alexBinos/tkl_keyboard/Mechanical/v0/tkl_bottom_middle.STL

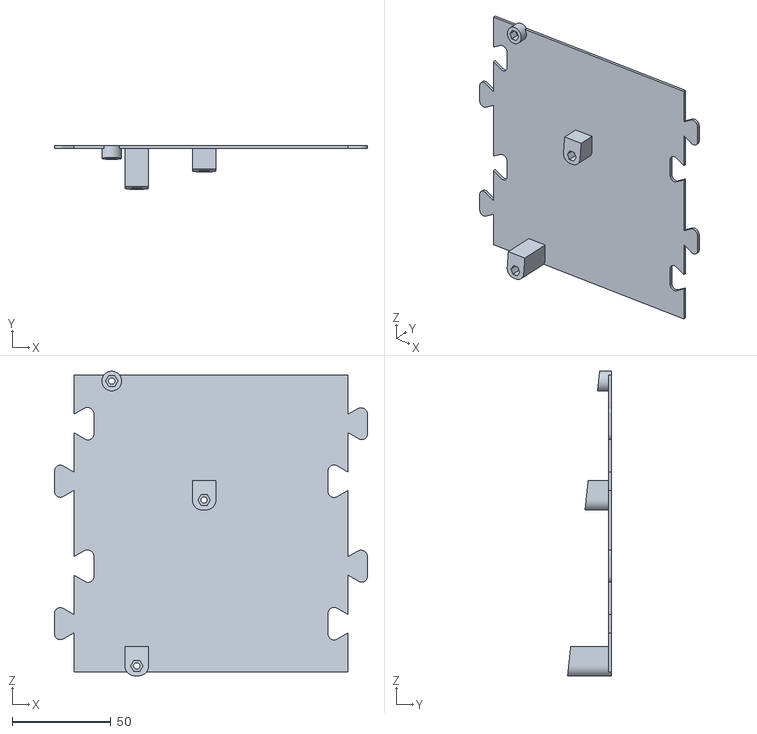
[picture p16: CAD file, 2022-05-21, an earlier design]
Mechanical/v0/tkl_bottom_middle.STL
158.7 x 22.2 x 154.5
