alexBinos/tkl_keyboard/Mechanical/v0/tkl_bottom_right.STL

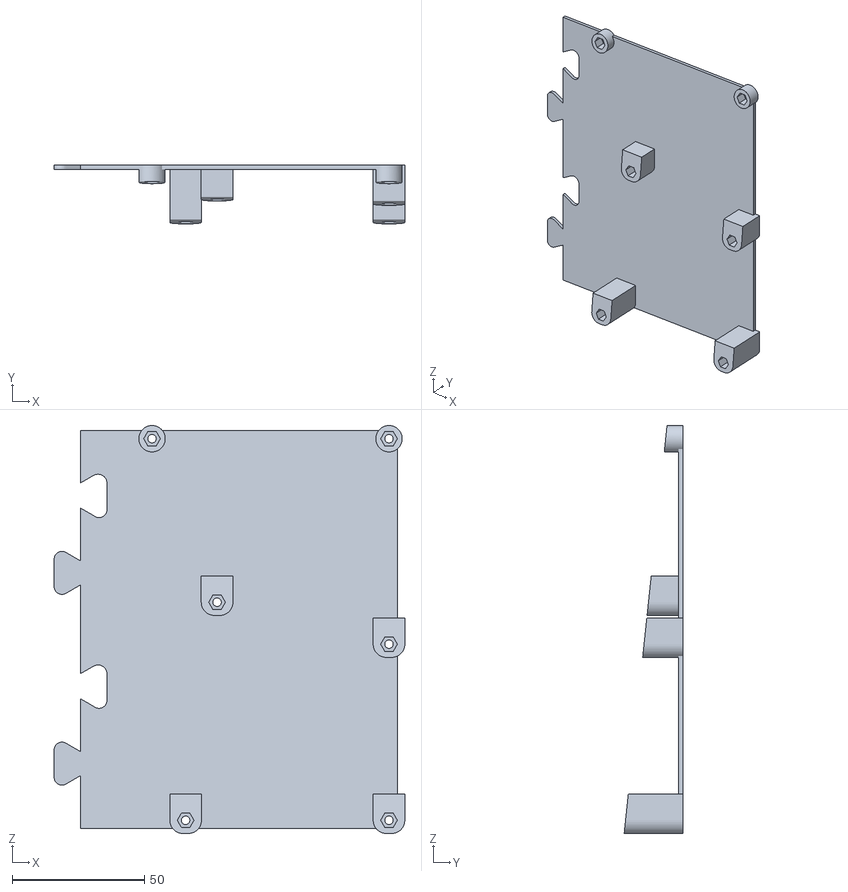
[picture p17: CAD file, 2022-05-21, an earlier design]
Mechanical/v0/tkl_bottom_right.STL
132.8 x 22.2 x 154.5
