alexBinos/tkl_keyboard/Mechanical/v0/tkl_key_frame_middle.STL

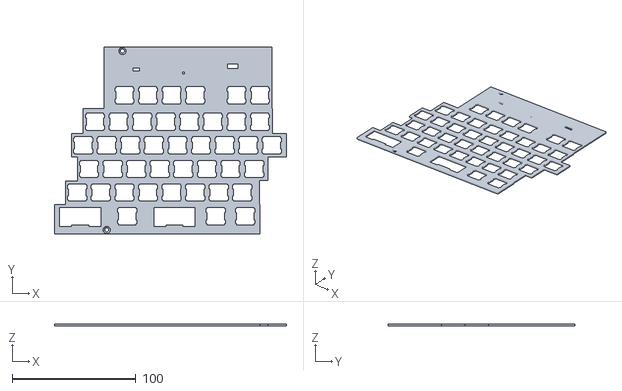
[picture p18: CAD file, 2022-05-21, an earlier design]
Mechanical/v0/tkl_key_frame_middle.STL
187.4 x 150.8 x 1.60
